salakrzy/HeishaMonBoth/assets/DIN_Case&Display.jpg

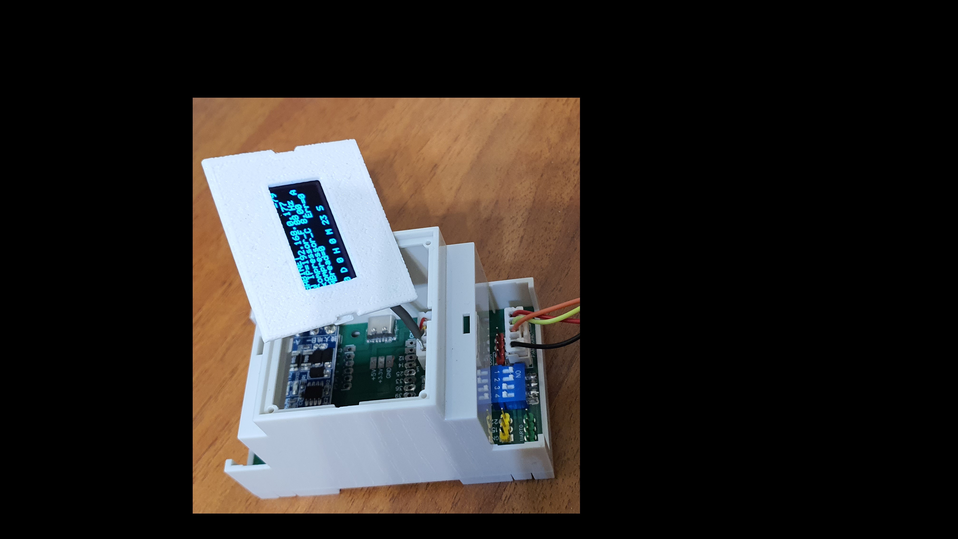
assets/DIN_Case&Display.jpg
