salakrzy/HeishaMonBoth/assets/HMBModbus.jpg

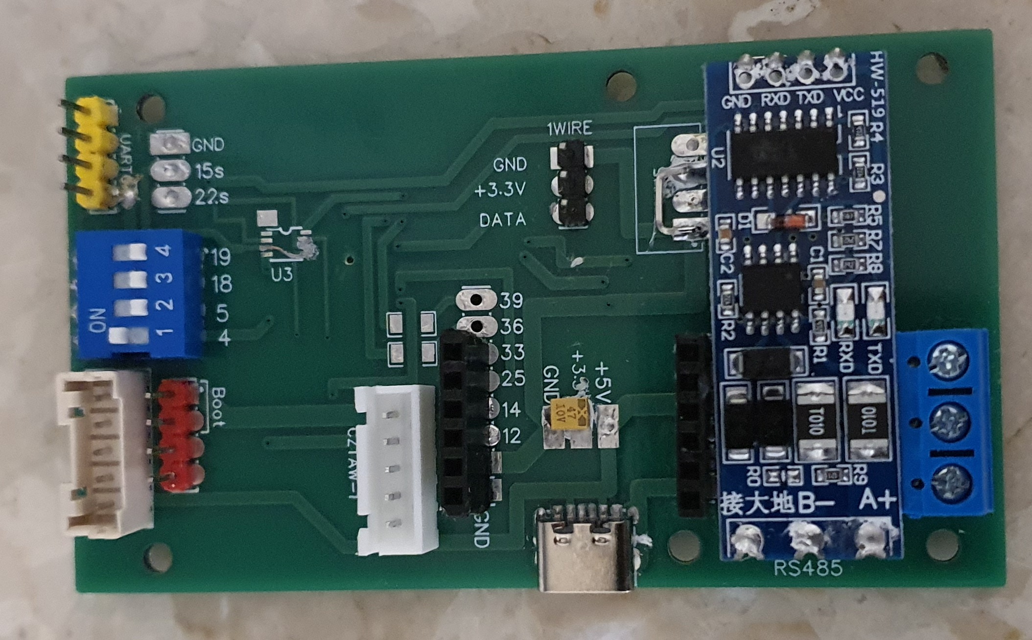
assets/HMBModbus.jpg
