salakrzy/HeishaMonBoth/Doc/Board set in Boot or Reset mode.jpg

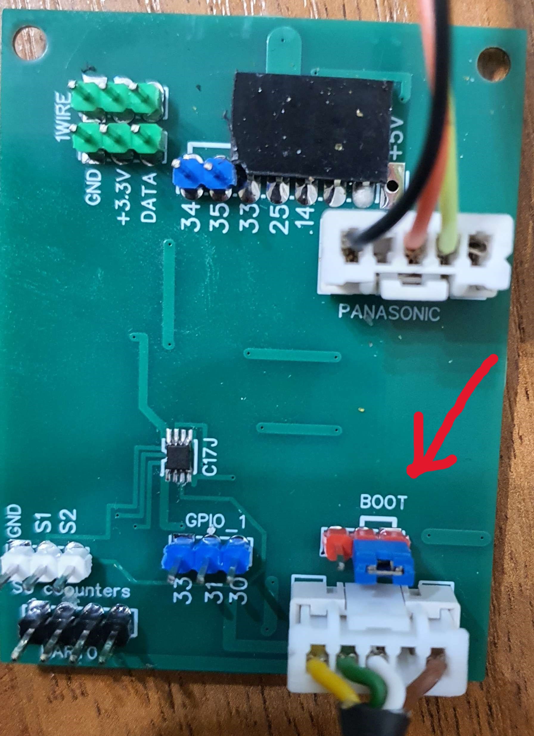
Doc/Board set in Boot or Reset mode.jpg
