salakrzy/HeishaMonBoth/Doc/Connection.png

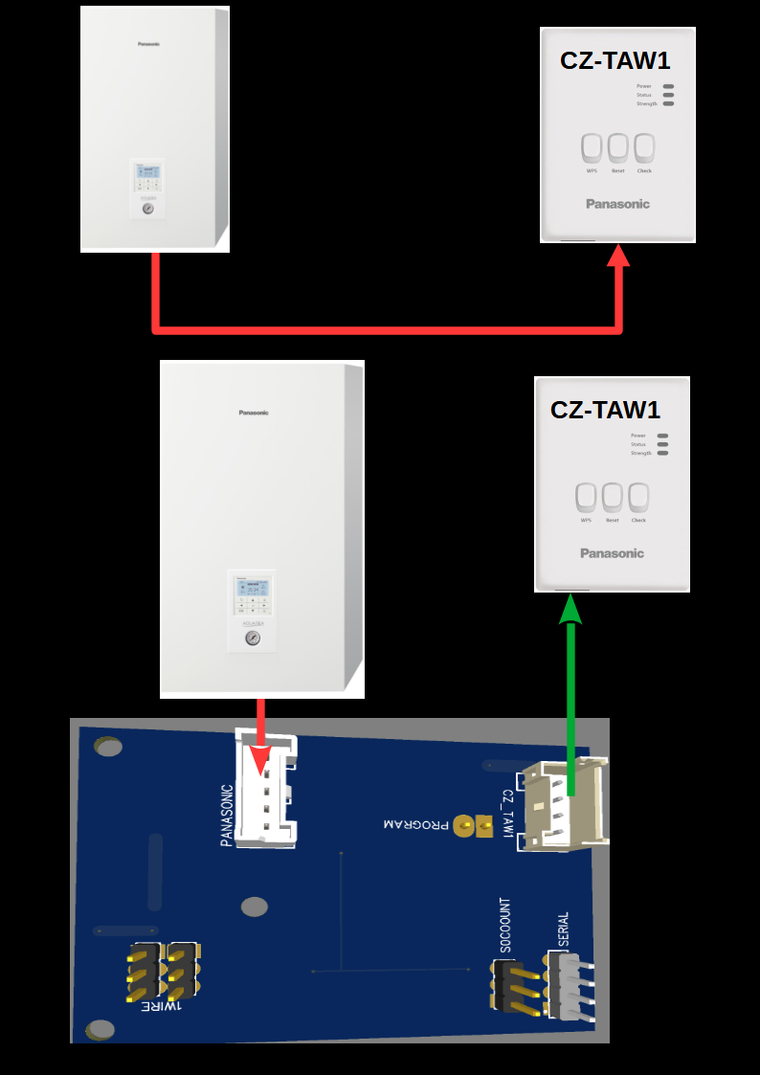
Doc/Connection.png
