salakrzy/HeishaMonBoth/Doc/HeishaMonBoth S Counters.png

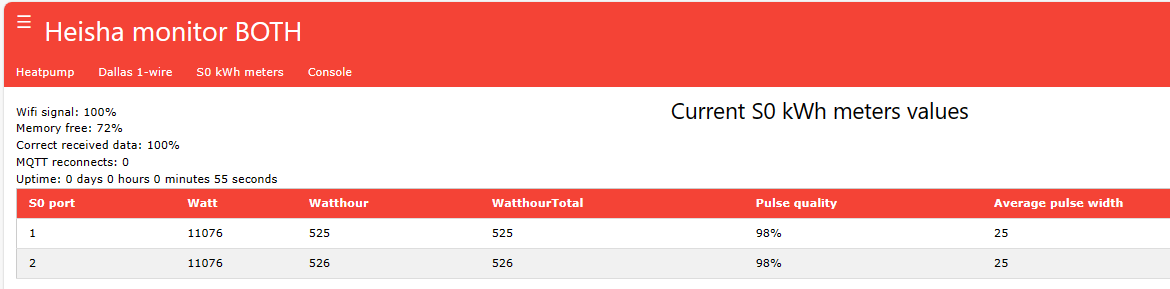
Doc/HeishaMonBoth S Counters.png
