salakrzy/HeishaMonBoth/Doc/HMBv3_8Console.PNG

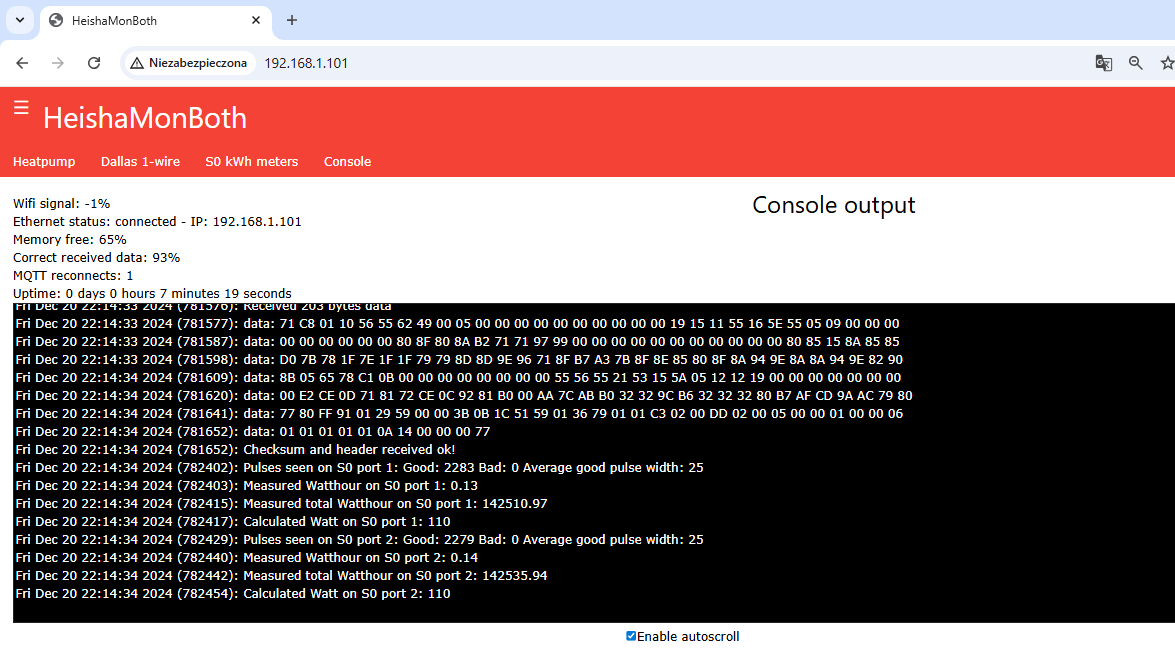
Doc/HMBv3_8Console.PNG
