salakrzy/HeishaMonBoth/Doc/HMBv3_8Dallas.PNG

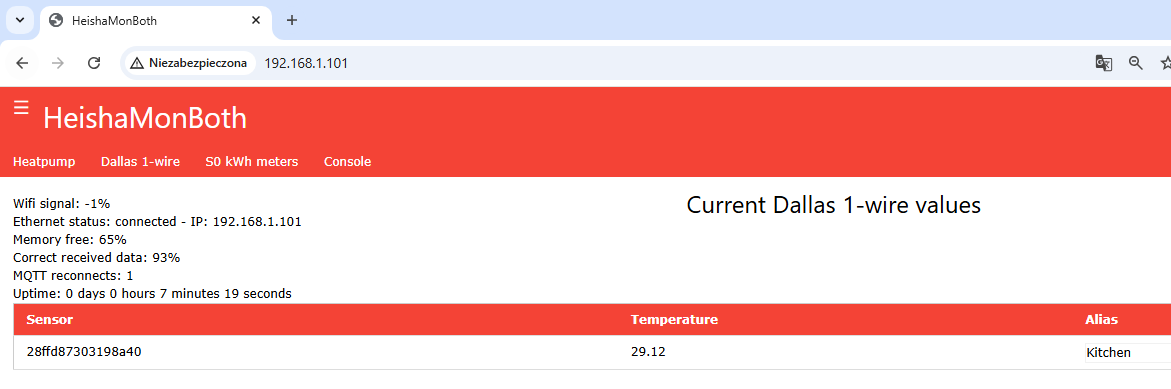
Doc/HMBv3_8Dallas.PNG
