salakrzy/HeishaMonBoth/Doc/HMBv3_8MainMenu.PNG

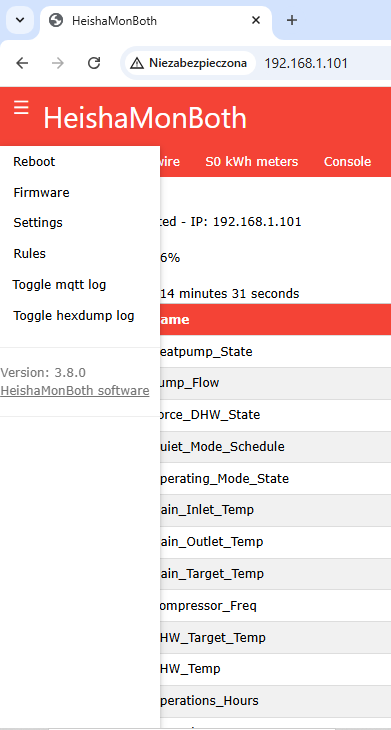
Doc/HMBv3_8MainMenu.PNG
