salakrzy/HeishaMonBoth/Doc/HMBv3_8Stetting1.png

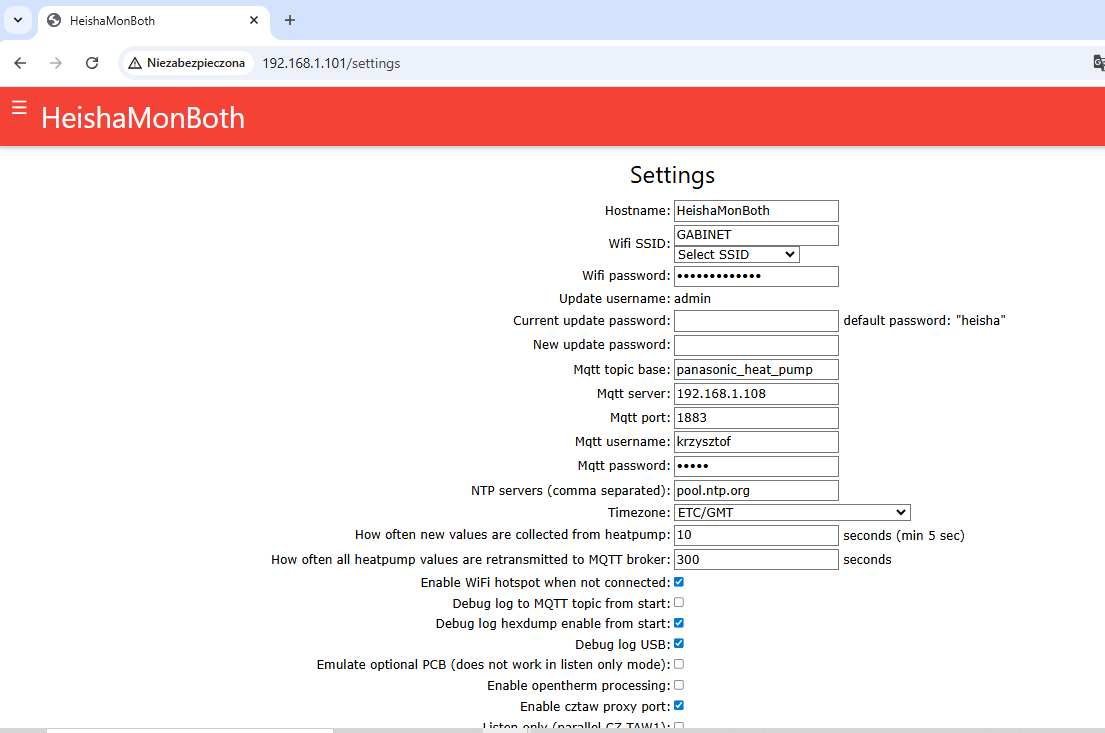
Doc/HMBv3_8Stetting1.png
