salakrzy/HeishaMonBoth/Doc/HMBv3_8Stetting2.png

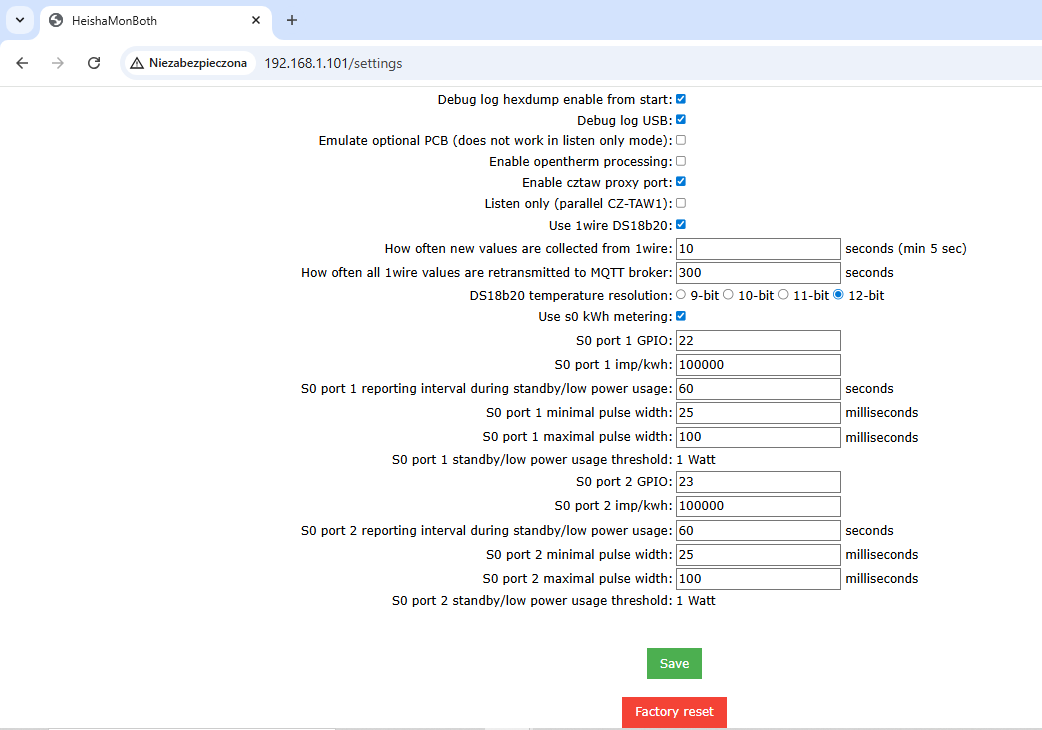
Doc/HMBv3_8Stetting2.png
