salakrzy/HeishaMonBoth/Doc/HMBv3_8Topics1.PNG

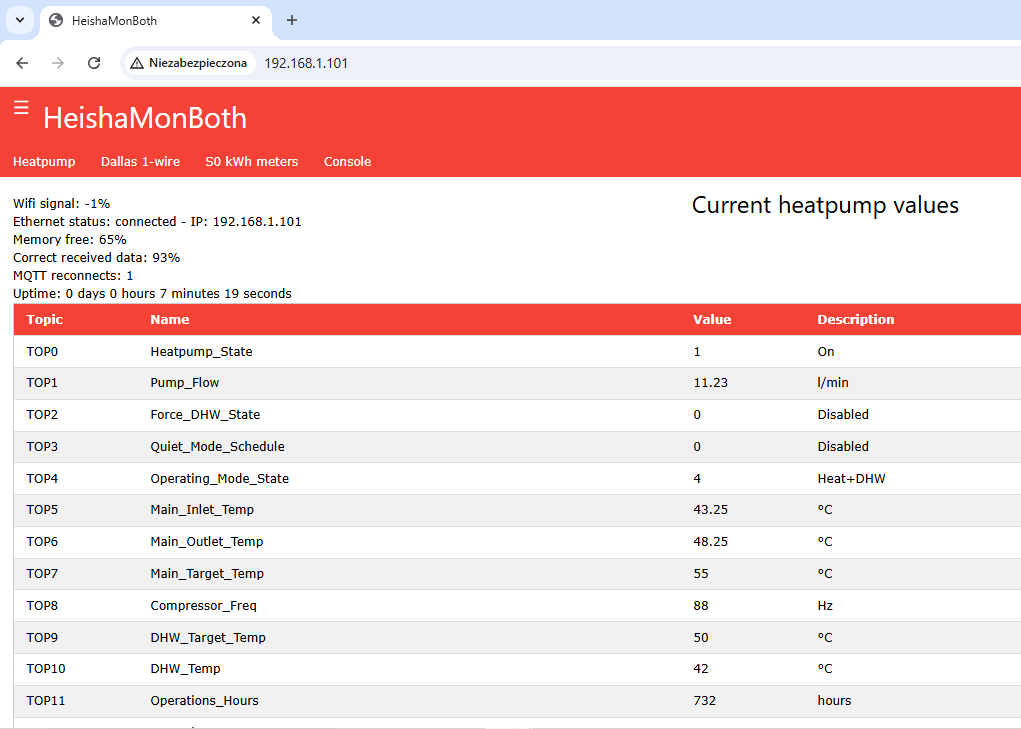
Doc/HMBv3_8Topics1.PNG
