salakrzy/HeishaMonBoth/Doc/HMBv3_9MainMenu.PNG

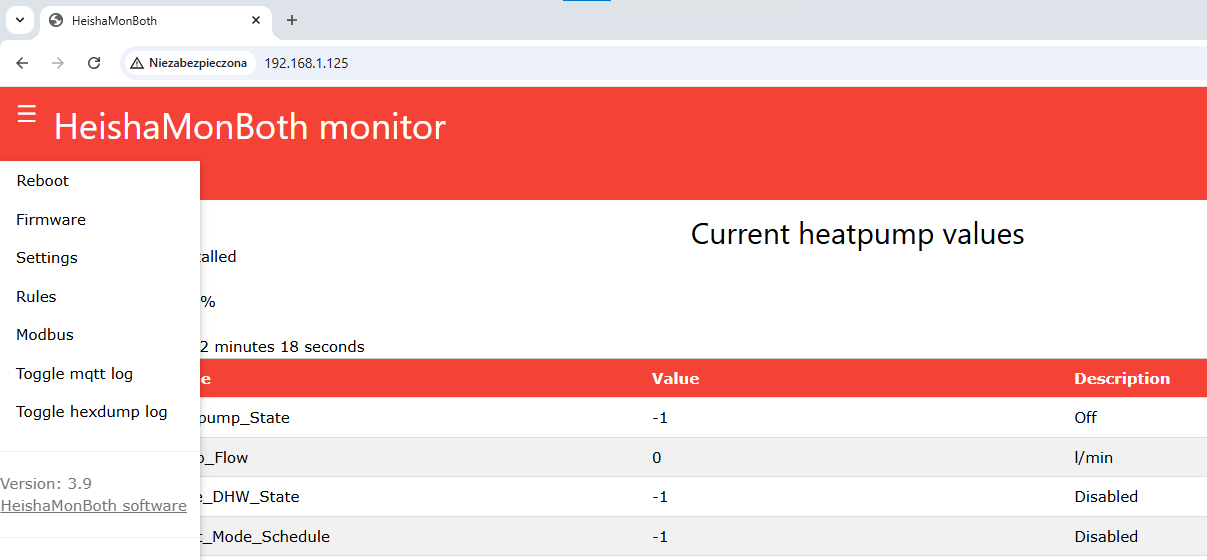
Doc/HMBv3_9MainMenu.PNG
