salakrzy/HeishaMonBoth/Doc/HMBv3_9Stetting.png

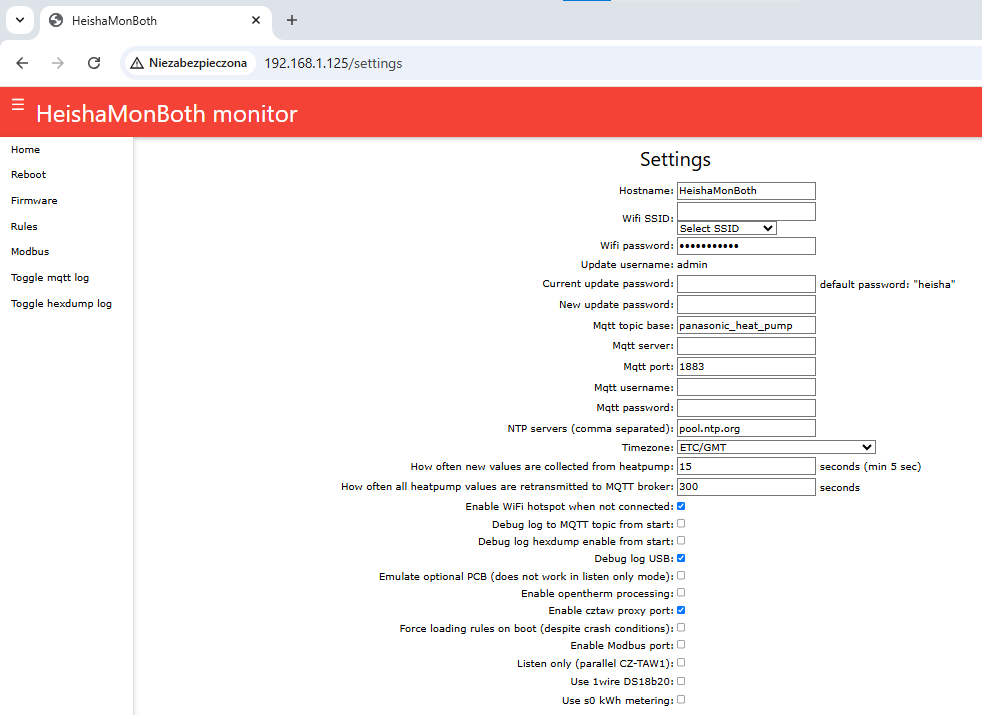
Doc/HMBv3_9Stetting.png
