salakrzy/HeishaMonBoth/Doc/HMBv3_9ViewFile.png

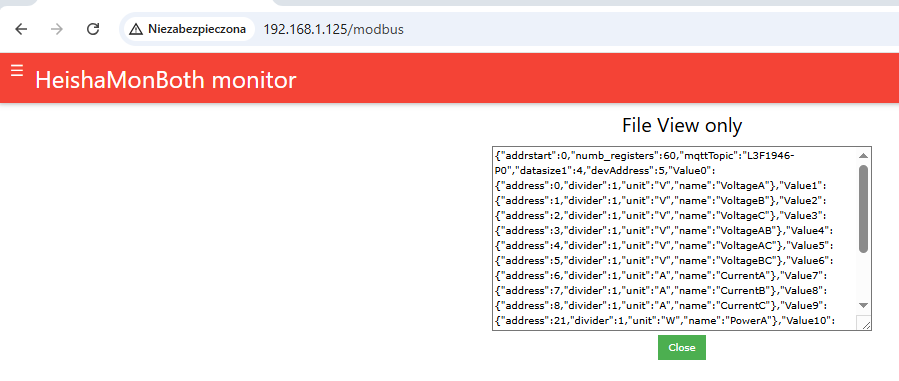
Doc/HMBv3_9ViewFile.png
