salakrzy/HeishaMonBoth/Doc/Modbus/assets/ModbusDEREconnection.jpg

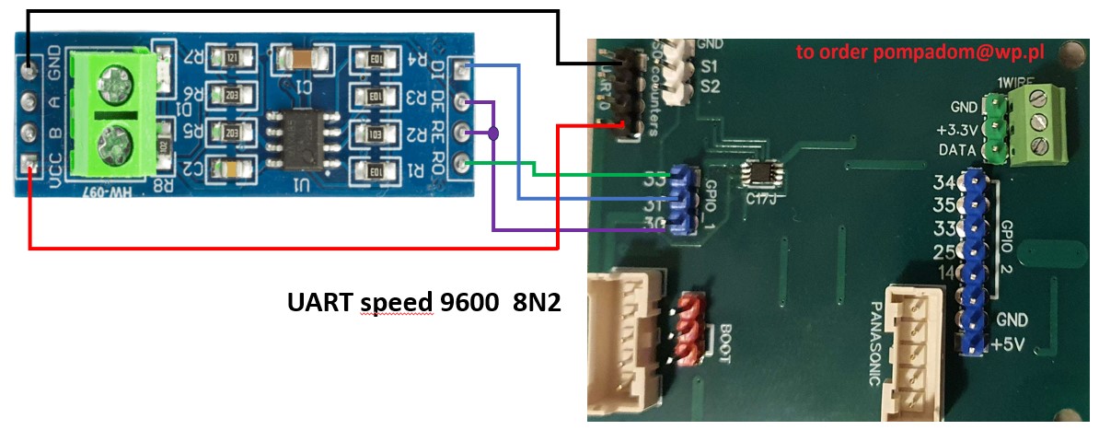
Doc/Modbus/assets/ModbusDEREconnection.jpg
