salakrzy/HeishaMonBoth/Doc/Modbus/RS85 connection UART softweare  version.png

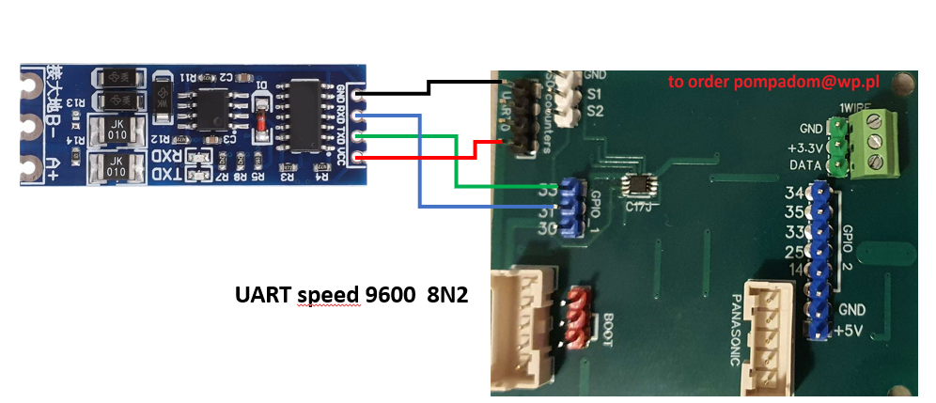
Doc/Modbus/RS85 connection UART softweare version.png
