salakrzy/HeishaMonBoth/Doc/new PCB/New_PCB.jpg

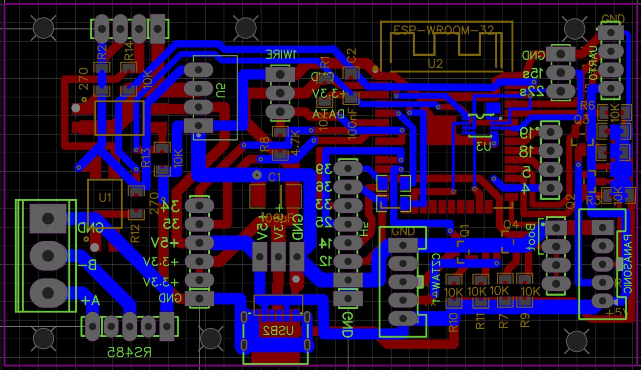
Doc/new PCB/New_PCB.jpg
