salakrzy/HeishaMonBoth/Doc/new PCB/New_PCB_Bottom1.jpg

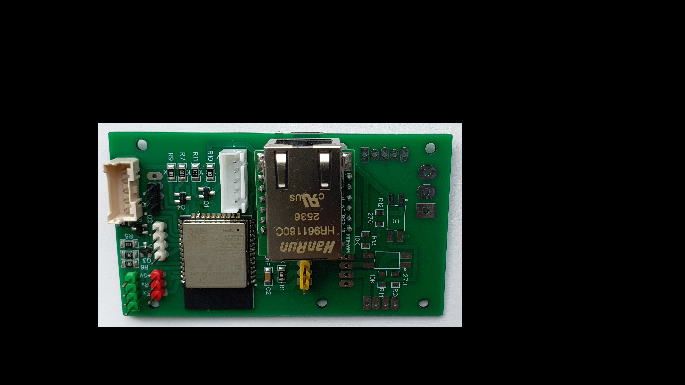
Doc/new PCB/New_PCB_Bottom1.jpg
