salakrzy/HeishaMonBoth/Doc/new PCB/New_PCB_Bottom.jpg

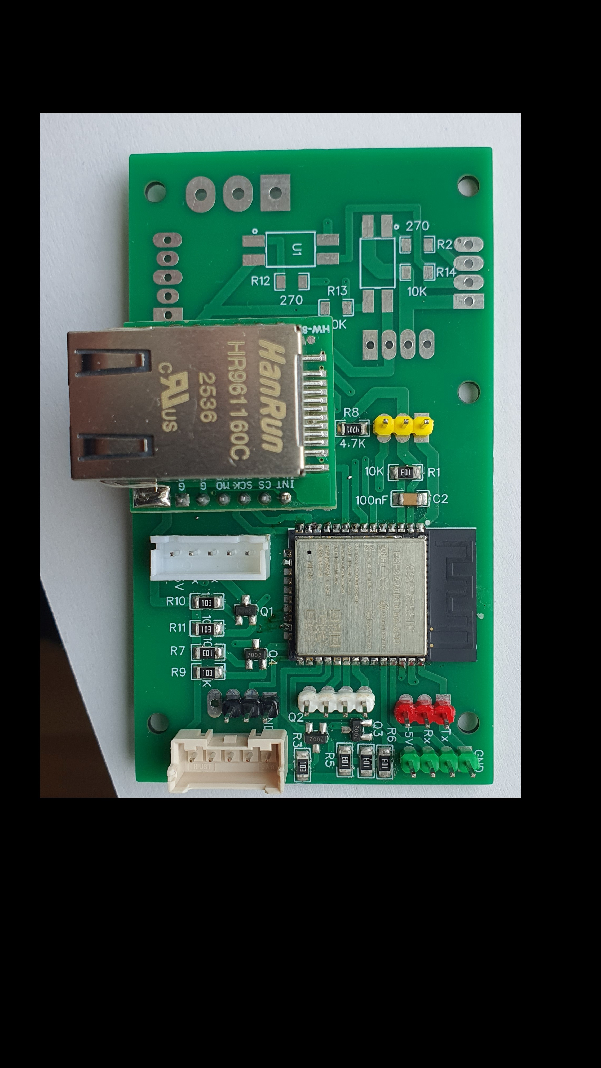
Doc/new PCB/New_PCB_Bottom.jpg
