salakrzy/HeishaMonBoth/Doc/new PCB/New_PCB_Top.jpg

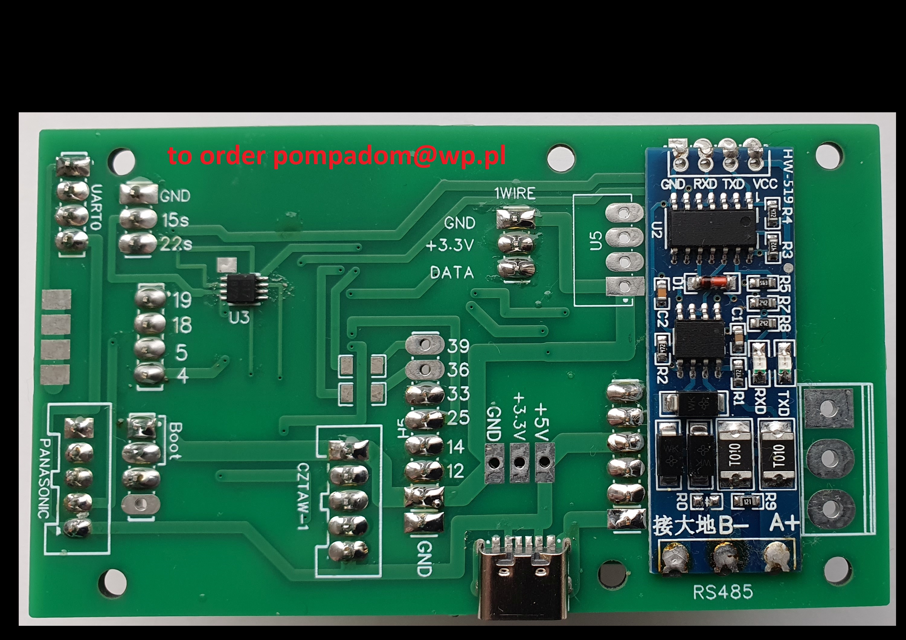
Doc/new PCB/New_PCB_Top.jpg
