salakrzy/HeishaMonBoth/Doc/new PCB/w5500 PinOut.png

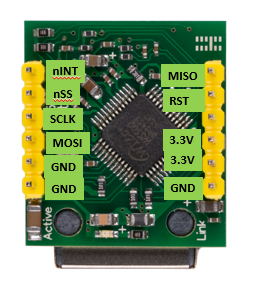
Doc/new PCB/w5500 PinOut.png
