salakrzy/HeishaMonBoth/Doc/new PCB/w5500 PinOutTop.png

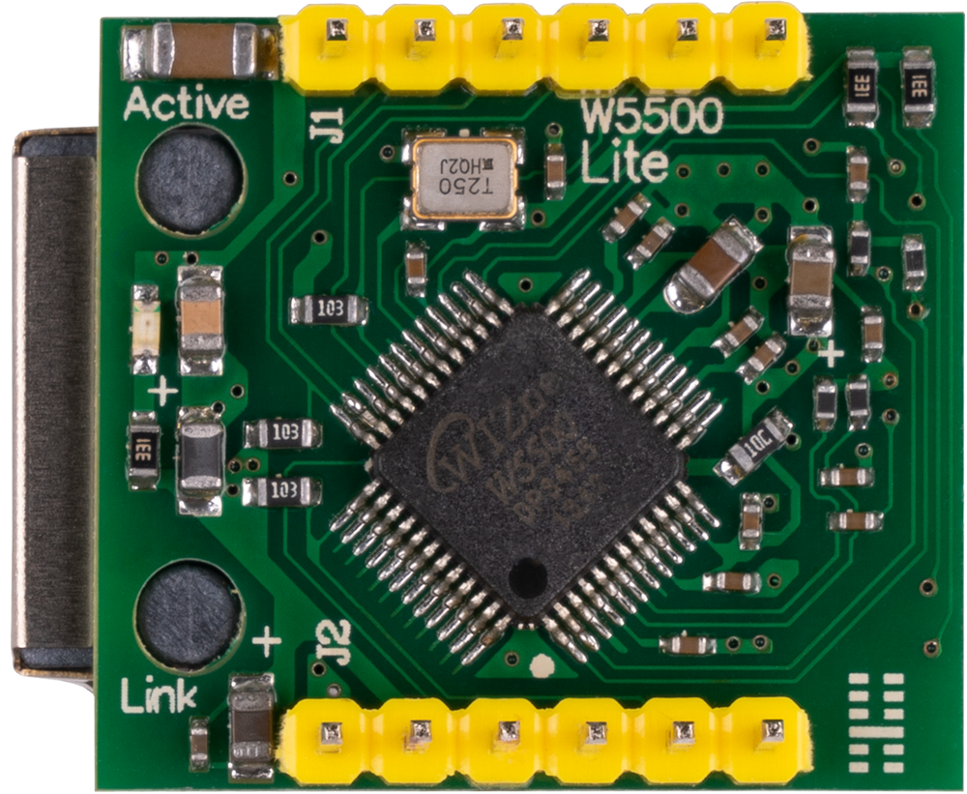
Doc/new PCB/w5500 PinOutTop.png
