salakrzy/HeishaMonBoth/Doc/new PCB/W5500 Top and Bottom mounted1.jpg

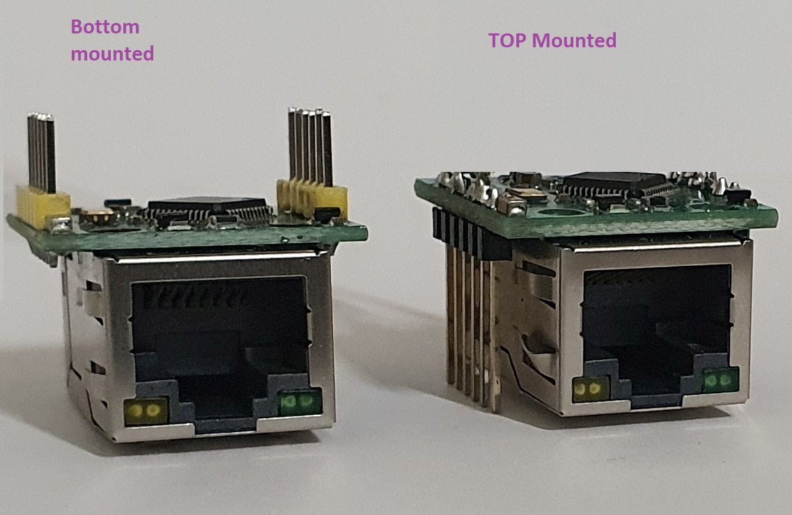
Doc/new PCB/W5500 Top and Bottom mounted1.jpg
