salakrzy/HeishaMonBoth/Doc/new PCB/W5500 Top and Bottom mounted.jpg

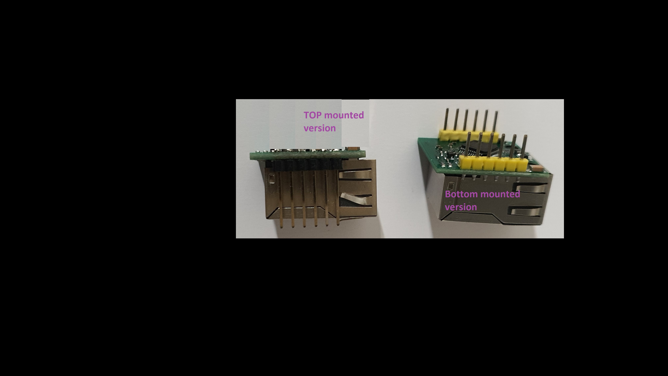
Doc/new PCB/W5500 Top and Bottom mounted.jpg
