salakrzy/HeishaMonBoth/Doc/PCB/Board3_8 correct Boot GPIO numbernew .PNG

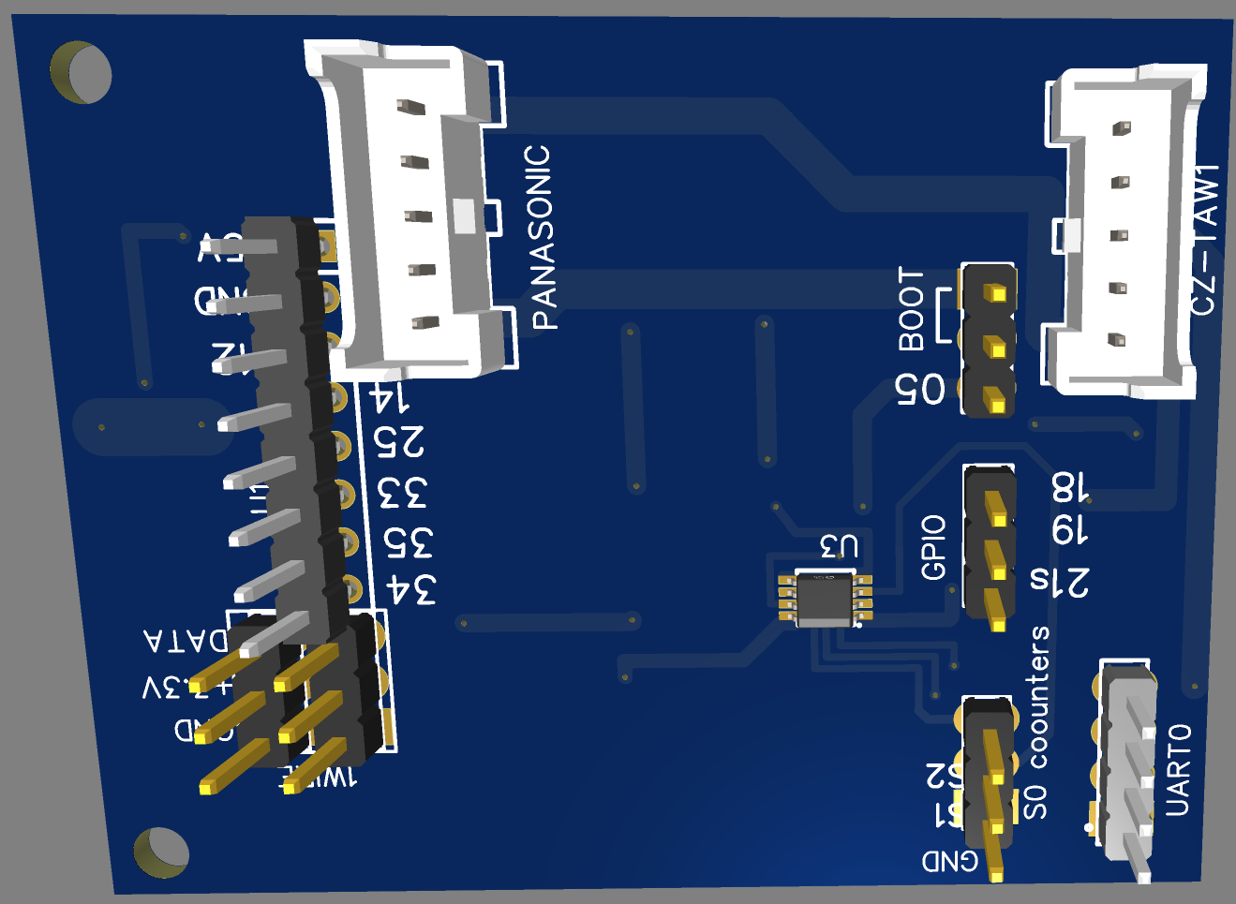
Doc/PCB/Board3_8 correct Boot GPIO numbernew .PNG
