salakrzy/HeishaMonBoth/Doc/PCB/Board3_8&Case.jpg

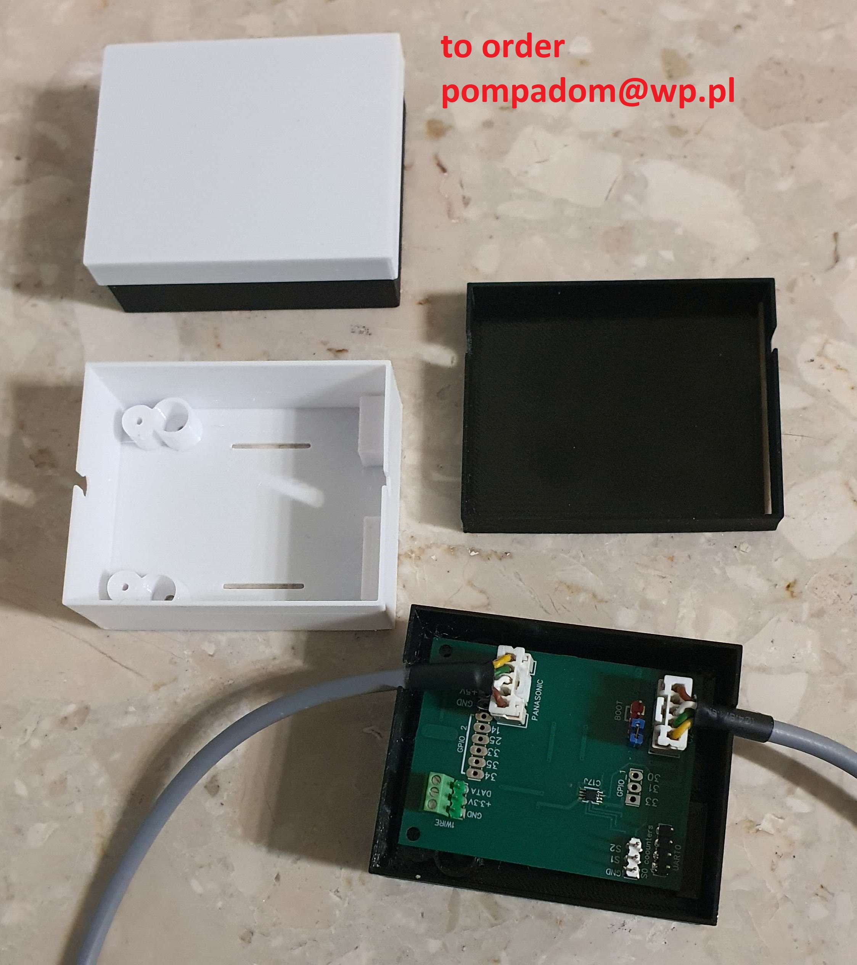
Doc/PCB/Board3_8&Case.jpg
