salakrzy/HeishaMonBoth/Doc/PCB/Board3_8Bottom.jpg

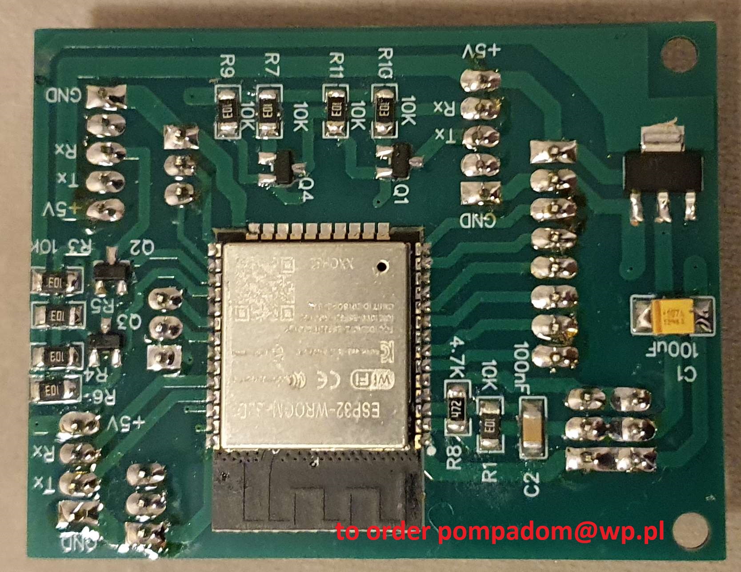
Doc/PCB/Board3_8Bottom.jpg
