salakrzy/HeishaMonBoth/Doc/PCB/Board3_8Top.jpg

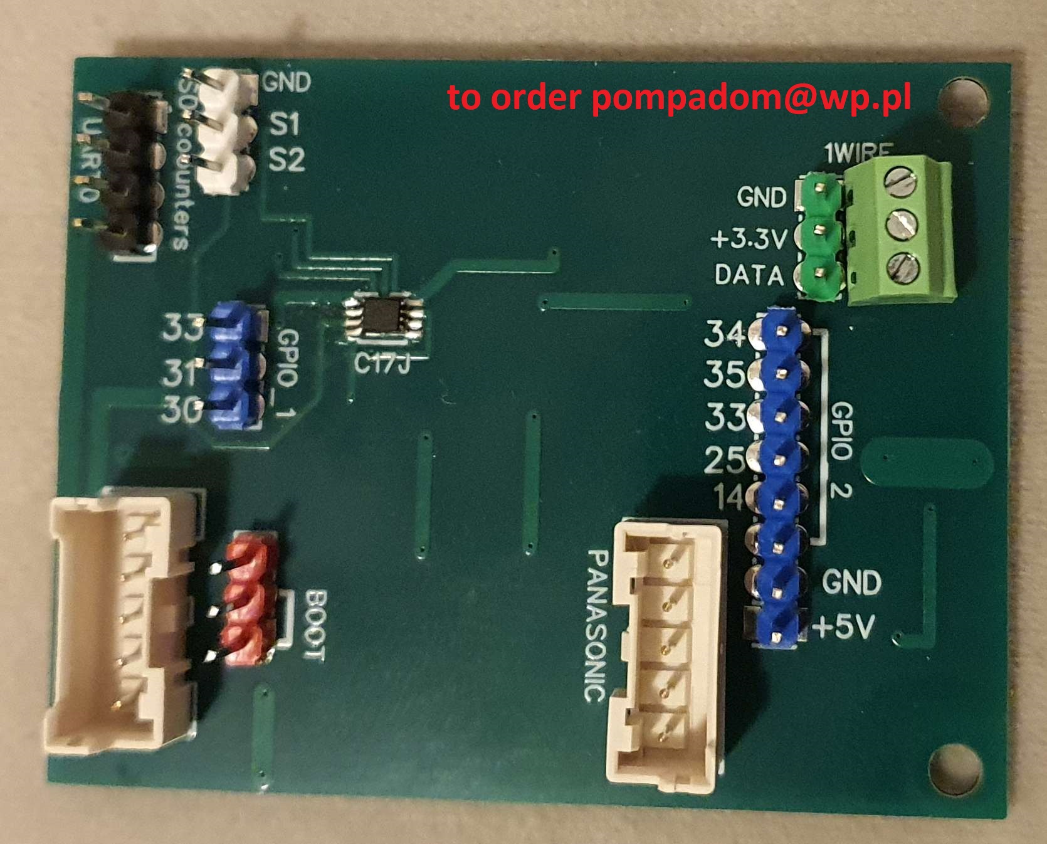
Doc/PCB/Board3_8Top.jpg
