salakrzy/HeishaMonBoth/Doc/PCB/HMBv3_8PCB.PNG

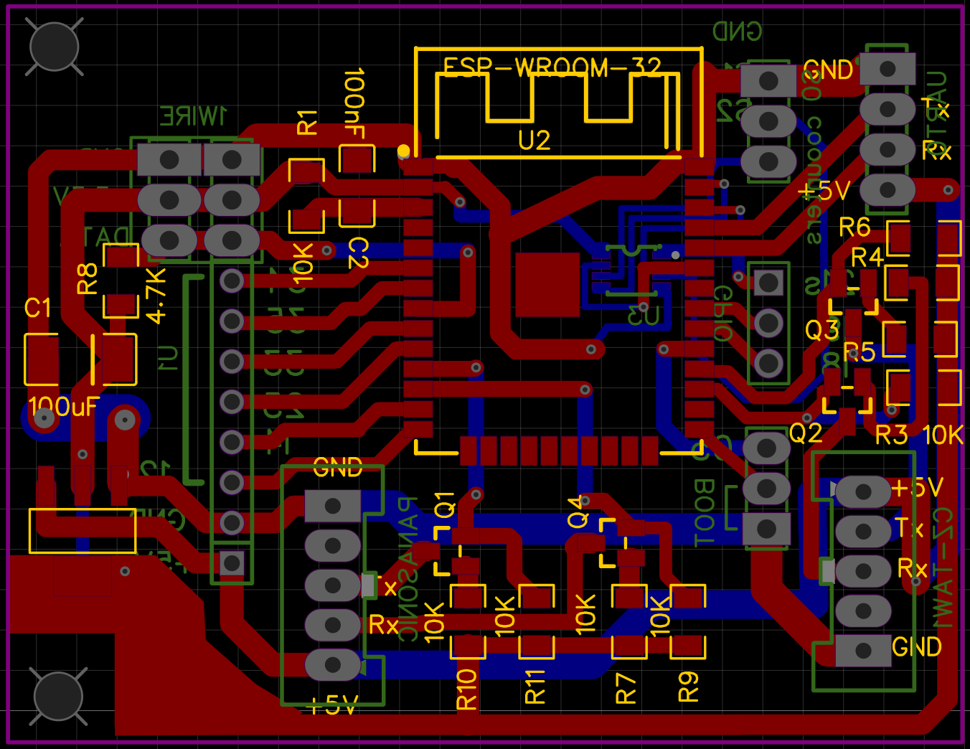
Doc/PCB/HMBv3_8PCB.PNG
