salakrzy/HeishaMonBoth/Doc/PCB/HMBv3_8SCH.PNG

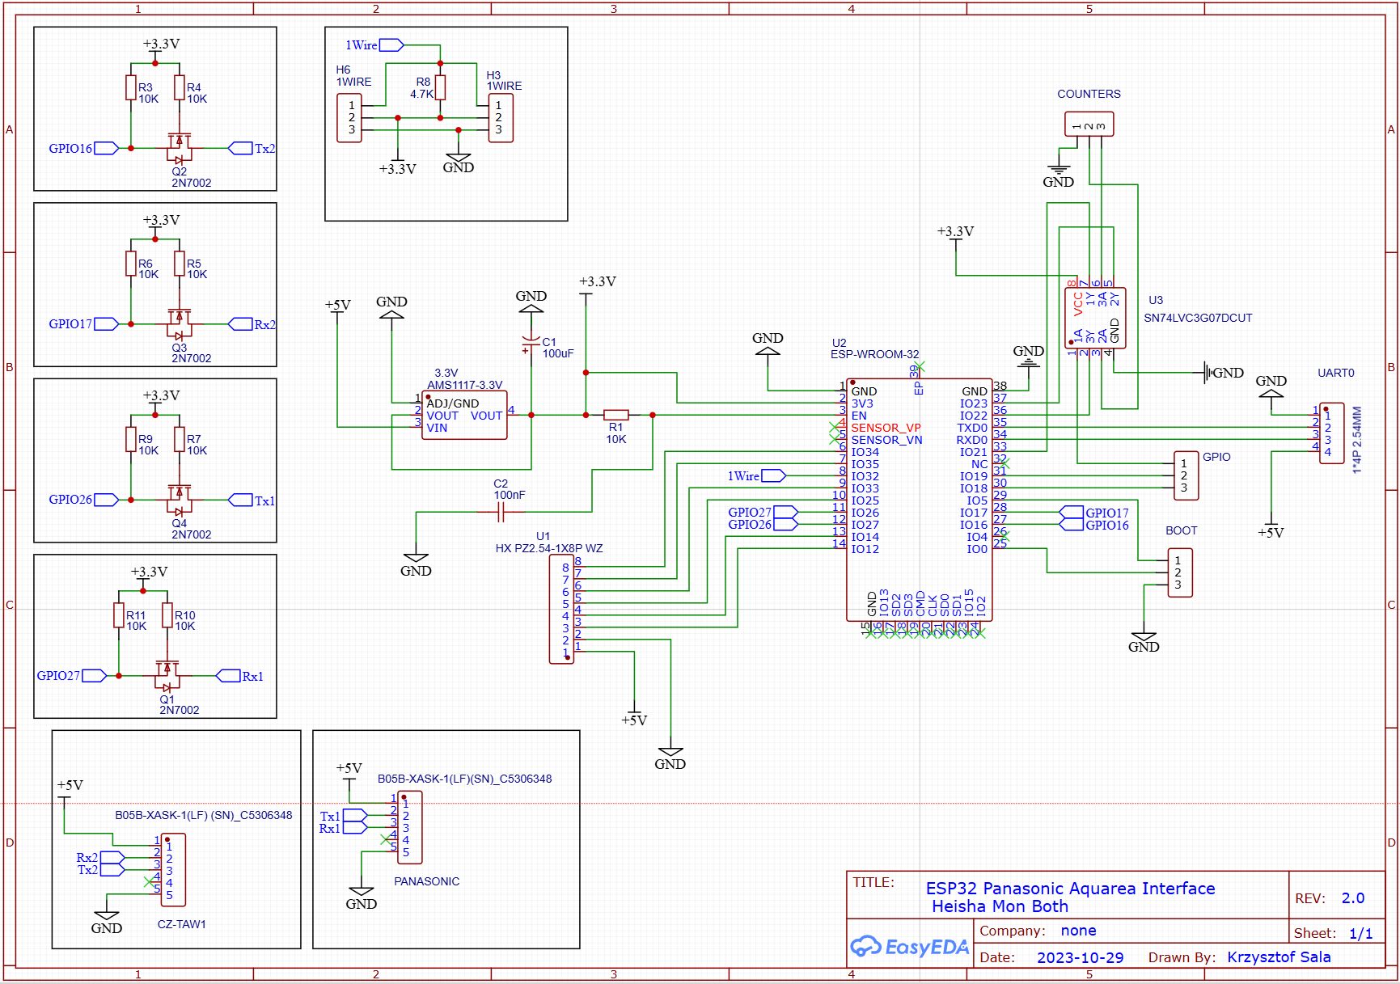
Doc/PCB/HMBv3_8SCH.PNG
