salakrzy/HeishaMonBoth/Doc/W5500 Ethernet connection/HMB Connecting_W5500 Ethernet module.PNG

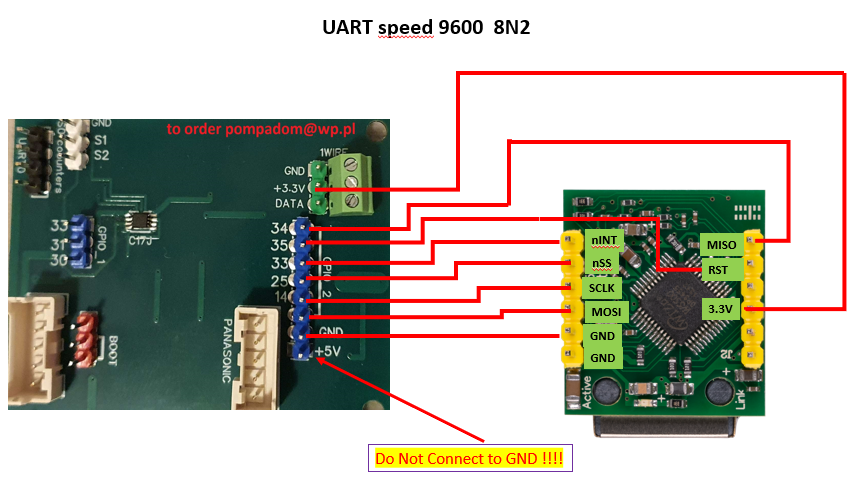
Doc/W5500 Ethernet connection/HMB Connecting_W5500 Ethernet module.PNG
