salakrzy/HeishaMonBoth/Doc/W5500 Ethernet connection/W5500 top View.png

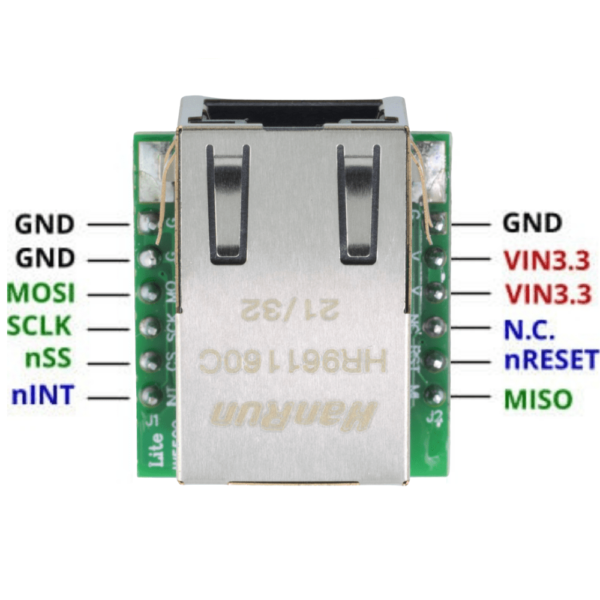
Doc/W5500 Ethernet connection/W5500 top View.png
