salakrzy/HeishaMonBoth/Doc/Modbus/assets/RS485ChangesDescription.png

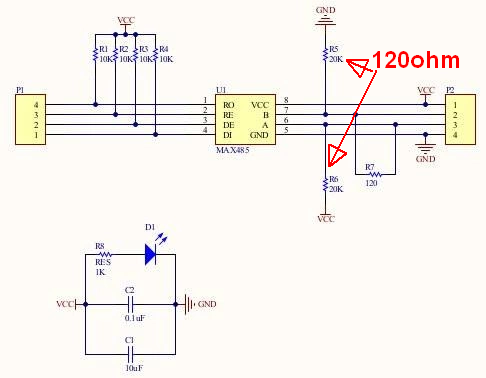
Doc/Modbus/assets/RS485ChangesDescription.png
