salakrzy/HeishaMonBoth/src/s0.h

#include <PubSubClient.h>
#include "src/common/webserver.h"

#define NUM_S0_COUNTERS 2

struct s0SettingsStruct {
  byte gpiopin = 255;
  unsigned int ppkwh = 1000; //pulses per Wh of the connected meter
  unsigned int lowerPowerInterval = 60; //configurabel low power interval
  unsigned int minimalPulseWidth = 25; //configurabel minimal s0 pulse width
  unsigned int maximalPulseWidth = 100; //configurabel maximal s0 pulse width
};

struct s0DataStruct {
  unsigned int pulses = 0; //number of pulses since last report
  unsigned int pulsesTotal = 0; //total pulses measured from begin
  unsigned int watt = 0; //calculated average power
  unsigned long lastPulse = 0; //last pulse in millis
  unsigned long nextReport = 0; //next time we reported the s0 value in millis
  unsigned long goodPulses = 0;
  unsigned long badPulses = 0;
  unsigned int avgPulseWidth = 0;
};

void initS0Sensors(s0SettingsStruct s0Settings[],bool newPCB);
void restore_s0_Watthour(int s0Port, float watthour);
void s0Loop(PubSubClient &mqtt_client, void (*log_message)(char*), char* mqtt_topic_base, s0SettingsStruct s0Settings[]);
void s0JsonOutput(struct webserver_t *client);
